nnamon/BYOG_Shield/Arduino Prog Examples/SHIELD_8x8_ex1/S8x8_Lib.h

//===============================================================================================================================
// LED 8x8
//===============================================================================================================================
int pb1Pin = 5;
int pb2Pin = 6;
int ledPin = 10;

int latchPin = 7;
int clockPin = 8;
int dataPin = 9;

const char data[][8] ={
{0B00000000, 0B00000000, 0B00000000, 0B00000000, 0B00000000, 0B00000000, 0B00000000, 0B00000000},
{0B00000100, 0B00000100, 0B00000100, 0B00000100, 0B00000100, 0B00000100, 0B00000000, 0B00000100},
{0B00001010, 0B00001010, 0B00001010, 0B00000000, 0B00000000, 0B00000000, 0B00000000, 0B00000000},
{0B00000000, 0B00001010, 0B00011111, 0B00001010, 0B00011111, 0B00001010, 0B00011111, 0B00001010},
{0B00000111, 0B00001100, 0B00010100, 0B00001100, 0B00000110, 0B00000101, 0B00000110, 0B00011100},
{0B00011001, 0B00011010, 0B00000010, 0B00000100, 0B00000100, 0B00001000, 0B00001011, 0B00010011},
{0B00000110, 0B00001010, 0B00010010, 0B00010100, 0B00001001, 0B00010110, 0B00010110, 0B00001001},
{0B00000100, 0B00000100, 0B00000100, 0B00000000, 0B00000000, 0B00000000, 0B00000000, 0B00000000},
{0B00000010, 0B00000100, 0B00001000, 0B00001000, 0B00001000, 0B00001000, 0B00000100, 0B00000010},
{0B00001000, 0B00000100, 0B00000010, 0B00000010, 0B00000010, 0B00000010, 0B00000100, 0B00001000},
{0B00010101, 0B00001110, 0B00011111, 0B00001110, 0B00010101, 0B00000000, 0B00000000, 0B00000000},
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
void DisplayChar(char Data){
    for(int c=0;c<8;c++) {
      DRow[c] = data[Data-32][c];
    }    
}
//===============================================================================================================================
