nnamon/BYOG_Shield/Arduino Prog Examples/SHIELD_8x8_ex1/Animate.h

//===============================================================================================================================
// Animate
//===============================================================================================================================
const char square4[8] = {
 0B11111111,
 0B10000001,
 0B10000001,
 0B10000001,
 0B10000001,
 0B10000001,
 0B10000001,
 0B11111111
};

const char square3[8] = {
 0B00000000,
 0B01111110,
 0B01000010,
 0B01000010,
 0B01000010,
 0B01000010, 
 0B01111110,
 0B00000000 
};

const char square2[8] = {
 0B00000000,
 0B00000000,
 0B00111100,
 0B00100100,
 0B00100100,
 0B00111100,
 0B00000000,
 0B00000000 
};
const char square1[8] = {
 0B00000000,
 0B00000000,
 0B00000000,
 0B00011000,
 0B00011000,
 0B00000000,
 0B00000000,
 0B00000000 
};
const char blank[8] = {
 0B00000000,
 0B00000000,
 0B00000000,
 0B00000000,
 0B00000000,
 0B00000000,
 0B00000000,
 0B00000000 
};
const char tryme[8] = {
 0B01000010,
 0B10100101,
 0B01000010,
 0B00000000,
 0B00000000,
 0B01000010,
 0B00111100,
 0B00000000 
};

const int ASDelay = 100;
//===============================================================================================================================
void AnimateSquares(){
    for(int c=0;c<8;c++) {
      DRow[c] = square4[c];
    }  
    delay(ASDelay);
    
    for(int c=0;c<8;c++) {
      DRow[c] = square3[c];
    }  
    delay(ASDelay);
    
    for(int c=0;c<8;c++) {
      DRow[c] = square2[c];
    }  
    delay(ASDelay);
    
    for(int c=0;c<8;c++) {
      DRow[c] = square1[c];
    }  
    delay(ASDelay);
    
    for(int c=0;c<8;c++) {
      DRow[c] = square2[c];
    }  
    delay(ASDelay);
    
    for(int c=0;c<8;c++) {  
      DRow[c] = square3[c];
    }  
    delay(ASDelay);

}
//===============================================================================================================================
//===============================================================================================================================
